lrswss/co2ampel/3d-parts/inner-frame.png

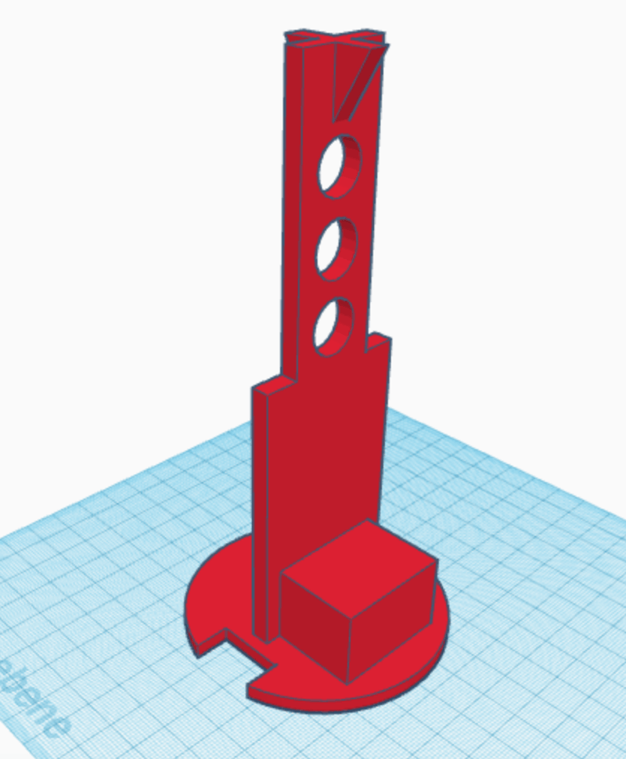
3d-parts/inner-frame.png
