lrswss/co2ampel/3d-parts/ventilation-grille.png

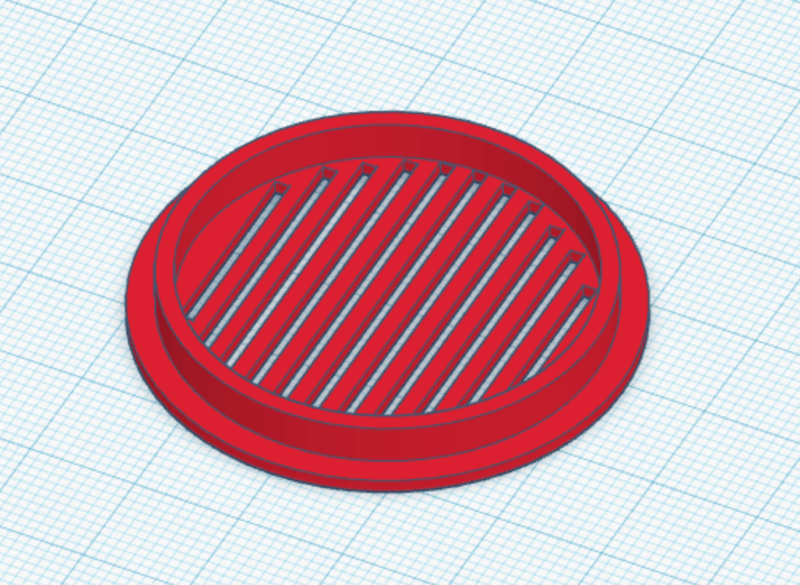
3d-parts/ventilation-grille.png
